Rune399/AEOM/reports and protocols/1. Drukken van knoppen report.pdf

# Drukken van knoppen report

### Sustainability @ Home

Onderzoekers:
Miro Mangelschots - Student Industrieel Ingenieur Industrieel Ontwerpen 2e bachelor Rune Coppieters - Student Industrieel Ingenieur Industrieel Ontwerpen 3e bachelor Kylian Maelstaf - Schakelstudent Industrieel Ingenieur Industrieel Ontwerpen

Zie “1. Drukken van knoppen protocol” voor meer detail over de gebruikte methode en artefacten in dit onderzoek.

# Resultaten

### Eerste eliminatie

Brushless motor: Vraagt veel extra componenten (ESC) en is beter voor toepassingen van hoge snelheid en lage krachtoverbrenging. De brushed DC motor heeft gelijkaardige eigenschappen, maar kan standaard met een tandwielkast geleverd worden, waardoor deze nog niet wordt uitgesloten.

### Testen

Brushed_motor test.mp4 (https://ugentbe-my.sharepoint.com/personal/kylian_maelstaf_ugent_be/Documents/Project%20gebruiksgericht%20ontwerpen/Sustainability%20@%20Home%20-%20Groepswerk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)
Lineair_actuator test.mp4 (https://ugentbe-my.sharepoint.com/personal/kylian_maelstaf_ugent_be/Documents/Project%20gebruiksgericht%20ontwerpen/Sustainability%20@%20Home%20-%20Groepswerk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)
Servo test1.mp4 (https://ugentbe-my.sharepoint.com/personal/kylian_maelstaf_ugent_be/Documents/Project%20gebruiksgericht%20ontwerpen/Sustainability%20@%20Home%20-%20Groepswerk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)
Solenoïde test.mp4 (https://ugentbe-my.sharepoint.com/personal/kylian_maelstaf_ugent_be/Documents/Project%20gebruiksgericht%20ontwerpen/Sustainability%20@%20Home%20-%20Groepswerk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)

# Conclusies

De solenoïde kan makkelijk uitgesloten worden, aangezien dit de enige oplossing was die de knop niet kon indrukken.
De servo heeft maar een matige krachtoverbrenging, voor een matig gewicht en matig gemak van aansturen. De servo is over het algemeen matig, waardoor deze wordt uitgesloten. Het voornaamste voordeel van de servo is echter de aanwezige feedbackloop, die voor hoge precisie en herhaalbaarheid zorgt. Dit weegt echter niet genoeg door, om dit component te kiezen.
De stepper motor wordt uitgesloten, door zijn complexe aansturing en gewicht. De stepper is beter geschikt voor toepassingen waar hoge precisie vereist is (in combinatie met snelheid en >360° draaien).

De lineaire actuator en Brushed DC motor blijven over van oplossingen die zouden volstaan voor de toepassing van knoppen indrukken. Dit is opzig relatief logisch, aangezien de lineaire actuator, in deze proef, een toegepast mechanisme van de brushed DC motor was.
Wat echter wel opvalt bij de specificaties van de beide motoren, is dat de LEGO motor, die gebruikt werd bij de lineaire actuator, veel zwakker is dan de zwakste optie van de DC-motor. Daaruit kan geconcludeerd worden dat de lineaire actuator (= schroefdraad) een grotere krachtomzetting heeft dan het andere mechanisme (glijdend stuk, met off-centre wheel). Om een lager gewicht, voor dezelfde krachtuitvoering te verkrijgen zal de lineaire actuator dus beter zijn… Een bijkomend voordeel is dat lineaire actuator een groet bereik aan posities heeft, terwijl het andere mechanisme eigenlijk maar 2 posities heeft.
Er zal dus verder gewerkt worden met de lineaire actuator.
Kan knop indrukken? | Kracht | Feedbackloop | Gewicht | Gemak aansturen (extra componenten + code)
Servo | Ja | Matig | Ja => hoge precisie + herhaalbaarheid | Matig | Matig
Stepper (niet op knop getest) | ? (Waarschijnlijk) | Matig | Nee (Maar hoge precisie + herhaalbaarheid, bij geen slip) | Zwaar | Moeilijk
Solenoide | Nee | Laag | Nee (niet per se nodig) | Zwaar | Makkelijk
Lineaire actuator | Ja | Zeer Hoog | Nee | Matig | Makkelijk
Brushed + geared | Ja | Zeer Hoog | Nee | Zwaar | Makkelijk
