Rune399/AEOM/reports and protocols/Protocol interview after pivot.pdf

# Protocol user interview (after pivot)

### Sustainability @ Home

Onderzoekers:
Miro Mangelschots - Student Industrieel Ingenieur Industrieel Ontwerpen 2e bachelor Rune Coppieters - Student Industrieel Ingenieur Industrieel Ontwerpen 3

e bachelor
Kylian Maelstaf - Schakelstudent Industrieel Ingenieur Industrieel Ontwerpen

# Kadering en doelstelling

Dit project is begonnen met het thema duurzaam leven thuis, maar is voor ons geëvolueerd tot het automatiseren van “domme apparaten” na een pivot.
Nu hebben we beslist om de focus te verleggen naar de “knoppendrukker”, een toestel die apparaten kan in- / uitschakelen waar een simpele onderbreking van de stroom niet voldoende zou zijn, (zoals bijvoorbeeld bij slimme stekkers) die voordien een deel zou geweest zijn van een groter systeem.
In dit onderzoek willen we onze doelgroep veranderen en ons afvragen waarom deze doelgroep nood zou hebben aan dit apparaat, door middel van interviews waarin we het toestel bespreken en bevragen.
We willen hiermee de volgende onderzoeksvragen beantwoorden:
- Is er interesse in ons product?
- Waar zijn er mogelijkheden tot automatisatie?
- Waar zijn de pains in de automatisatie thuis?
- Is er een meerwaarde tegenover slimme stekkers?

# Verandering doelgroep

We gaan ons verdiepen op de algemene, grote groep mensen in bezit van zonnepanelen die simpelweg willen besparen en geen budget hebben voor batterijen.
Namelijk de mensen die graag hun huis zouden willen “hacken”, mensen die graag met gadgets en technische snufjes bezig zijn en interesse hebben in het automatiseren van hun huis.

# Methode

Gebruikte methodiek: User interview (N=3)
Gebruikte artefacten: Vragenlijst

# Werkwijze

Er zullen een aantal vragen gesteld worden die de volgende onzeker- / onduidelijkheden tracht aan te pakken:
- Zien de gebruikers een meerwaarde in het product, dewelke?
- Is er interesse in het product?
- Meerwaarde tegenover enkel slimme stekkers kopen?
- Wat maakt dit meer dan enkel een coole gadget?
- Hoeveel setuptijd is acceptabel?
- Hoe vaak zouden mensen iets willen automatiseren?
- Wat willen mensen automatiseren?
- Verkopen als bouwpakket?
- Pains identificeren waarop ingespeeld kan worden?
De onderzoeker stelt zicht voor en legt kort de bedoeling van het interview uit.
Bij elke vraag zal er indien mogelijk verdiept worden om de achterliggende intenties / gedachten in kaart te brengen.

## Brede vragen

- Heeft u interesse in het automatiseren van uw huis of bepaalde apparaten? Waarom?
- Bent u bereid hier actief oplossingen voor te zoeken of een artikel voor aan te schaffen?
- Bent u in bezit van voorprogrammeerbare toestellen?
- Indien ja, gebruikt u deze features vaak? Merkt u een aantal mogelijkse tekorten met dat systeem?
- Indien nee, waarom niet?
- Bij welke toestellen / systemen denkt u dat er verdere mogelijkheden zijn voor automatisatie?
- Ochtendroutine?
- Thuiskomen?
- s’ Avonds?
- Is de automatisering van uw wasmachine / droogkast iets die u nuttig zou vinden? Waarom?
- Hoe vaak en wanneer schakelt u deze toestellen in?
- Bent u in bezit van slimme stekkers?
- Waarom wel / niet?
- Merkt u hier beperkingen mee op?
- Zijn er toestellen bij u thuis die niet geautomatiseerd kunnen worden door slimme stekkers?
- (drukknoppen, draaiknoppen, …)
- Zijn er bezorgdheden rondom automatisatie in uw huishouden? Wat moet vermeden worden?
- Hoeveel controle wilt u behouden over automatische acties?
- Bent u actief bezig met het maximaliseren van de opgewekte zonne-energie?
- Schakelt u apparaten in tijdens dat de zon energie oplevert?
- Kunt u een voorbeeld geven van wanneer u uw gedrag aanpast aan zonne-energie?
- Zou u een apparaat die u hierbij helpt effectief gebruiken?

## Gerichte vragen

Hier zullen we een aantal foto’s voorleggen van de knoppendrukker als concept, om een beeld te scheppen over het product.
- Wat zou u ervan vinden moest een toestel fysiek de juiste knoppen drukken om apparaten in/uit te schakelen?
- Zou u zo’n systeem vertrouwen om zelfstandig iets aan / uit te zetten?
- In welke situatie zou dit systeem ongewenst zijn?
- Ziet u een meerwaarde in dit product tegenover slimme stekkers?
- Wat zou dit apparaat moeten doen zodat u het volledig zou vertrouwen?
- Welke zaken zouden het vertrouwen verbreken?
- Wat zou voor u een reden kunnen zijn om dit systeem niet te willen installeren?
- In welke situatie zou een slimme stekker voor u een betere optie zijn?
- Op welk apparaat zou u dit systeem als eerst willen gebruiken?
- Op welk apparaat zou u dit systeem absoluut niet willen toepassen? Waarom?
- Wilt u feedback krijgen over acties die het apparaat uitvoert?
- Indien ja, welke feedback zou relevant zijn? Voor, tijdens of na de actie?
- Indien nee, waarom niet?
- Hoeveel tijd zou u willen spenderen in de setup van dit apparaat?
- Bent u bereid om tools te gebruiken voor een eenmalige setup?
- Geen, meegeleverde of thuis beschikbare tools?
- Zou het interessant zijn om ons product aan te bieden als bouwpakket?
- Componenten apart (ikea)
- Uitbreidingspakket (met extra knoppencontrollers en dergelijke uitbeidingen)

## Concluderend

De onderzoeker rond het gesprek af en bedankt de respondent voor hun medewerking.

# Meting

Dit interview zal via audio opgenomen worden, wat achteraf samen met eventuele notities hernomen kan worden om gemiste items toch nog te vatten.

Zie de report (https://ugentbe-my.sharepoint.com/personal/kylian_maelstaf_ugent_be/Documents/Project%20gebruiksgericht%20ontwerpen/Sustainability%20@%20Home%20-%20Groepswerk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) voor de uitkomst en analyse van dit onderzoek.
