Rune399/AEOM/cad/rotating pivot arm/V2/adjusted.jpg

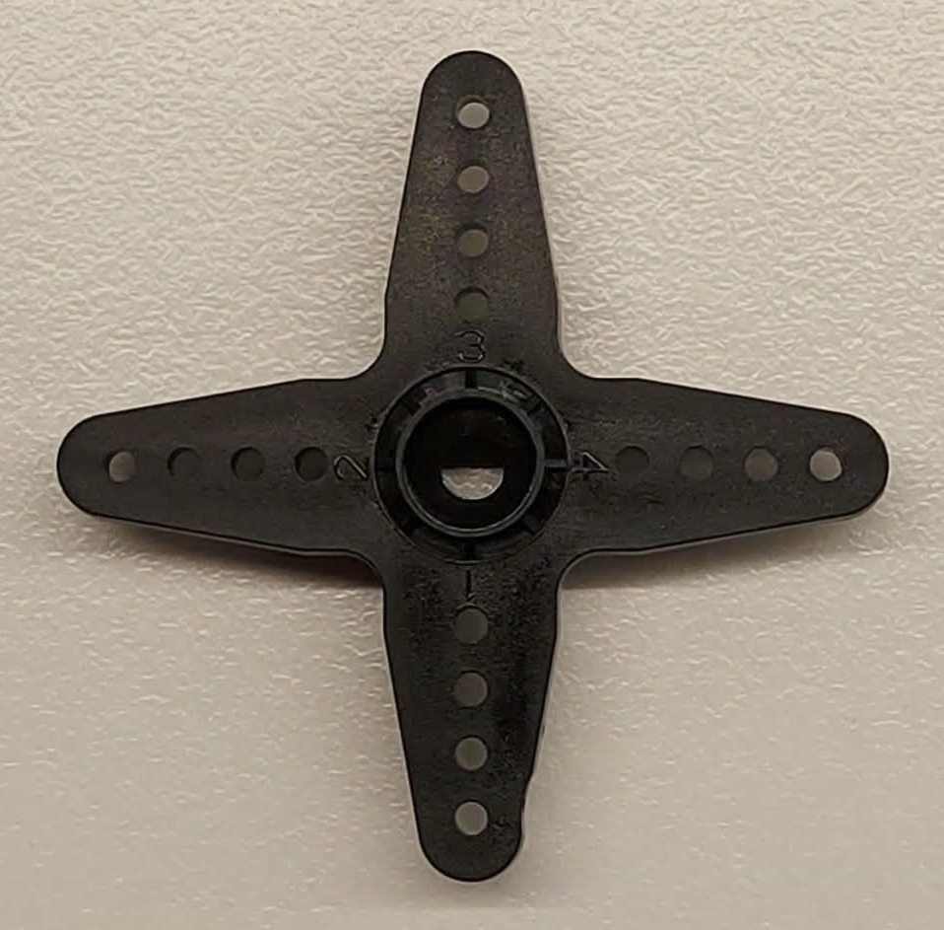
cad/rotating pivot arm/V2/adjusted.jpg
