Rune399/AEOM/img/CMF_Morfologische_kaart.jpg

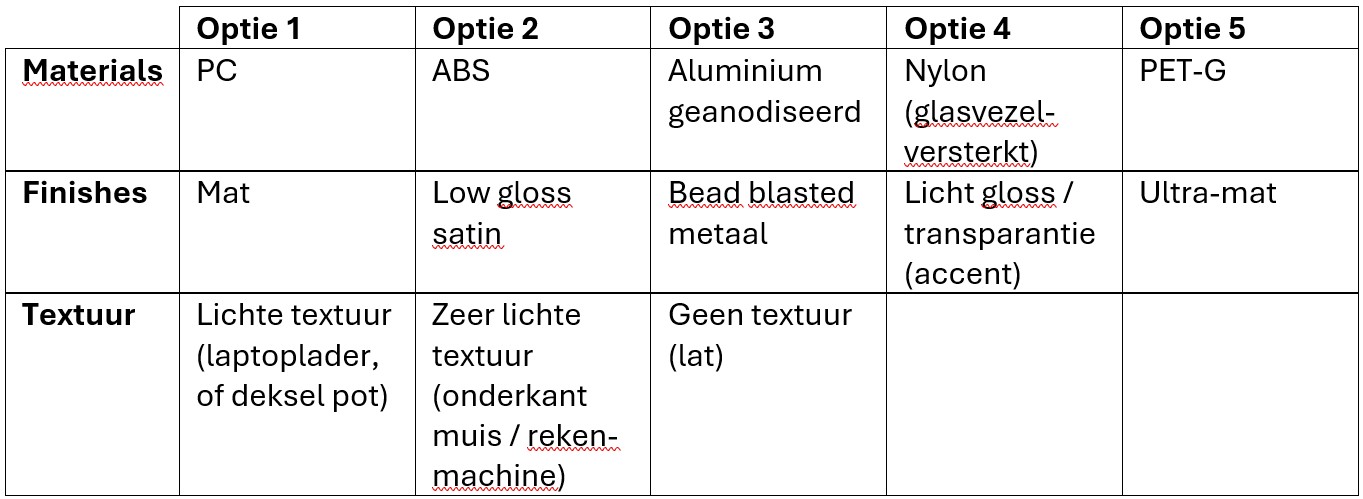
img/CMF_Morfologische_kaart.jpg
