Rune399/AEOM/img/Hero2.png

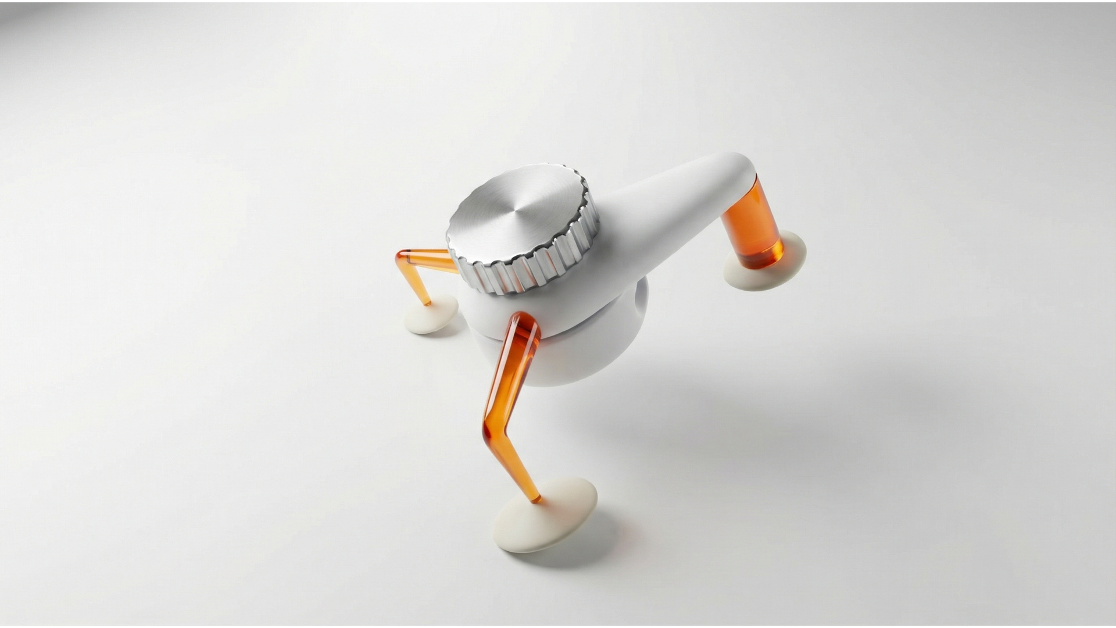
img/Hero2.png
