Rune399/AEOM/img/Interface1 pg3.jpg

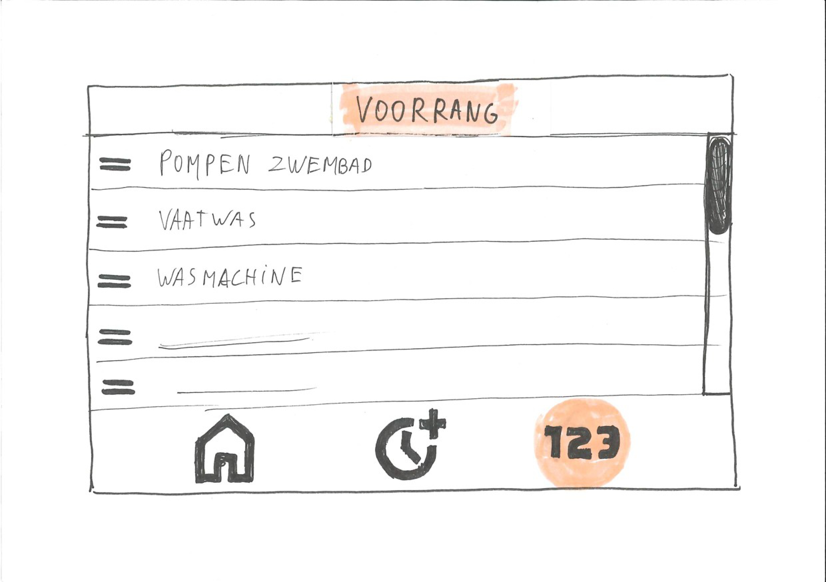
img/Interface1 pg3.jpg
