Rune399/AEOM/img/Interface3 pg1.jpg

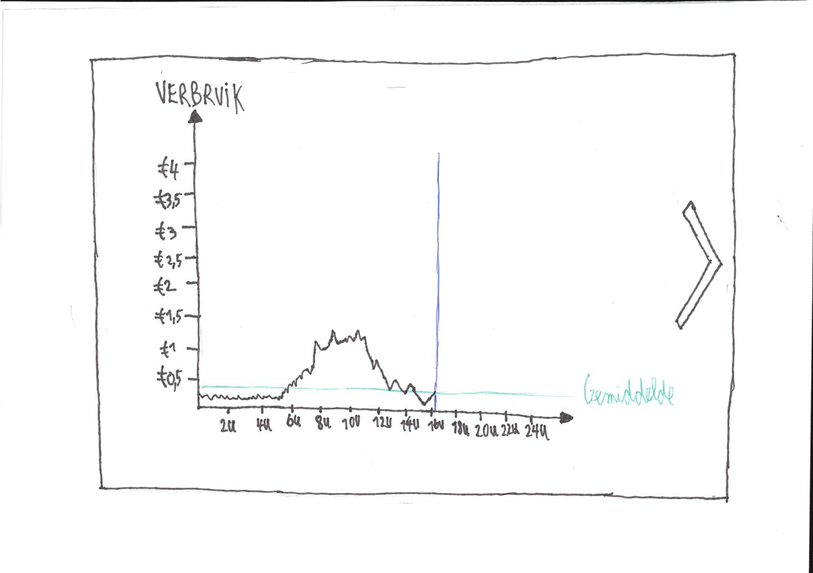
img/Interface3 pg1.jpg
