Rune399/AEOM/img/Interface3 pg3 V2.jpg

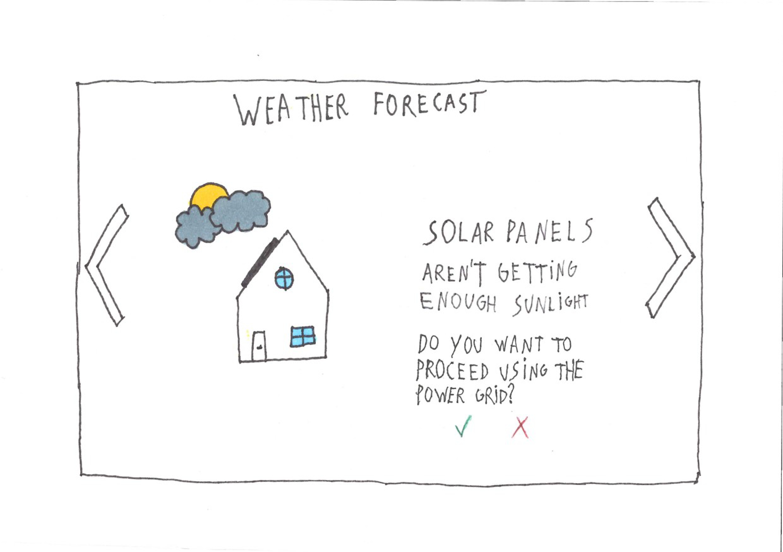
img/Interface3 pg3 V2.jpg
