Rune399/AEOM/img/Interface3 pg4.jpg

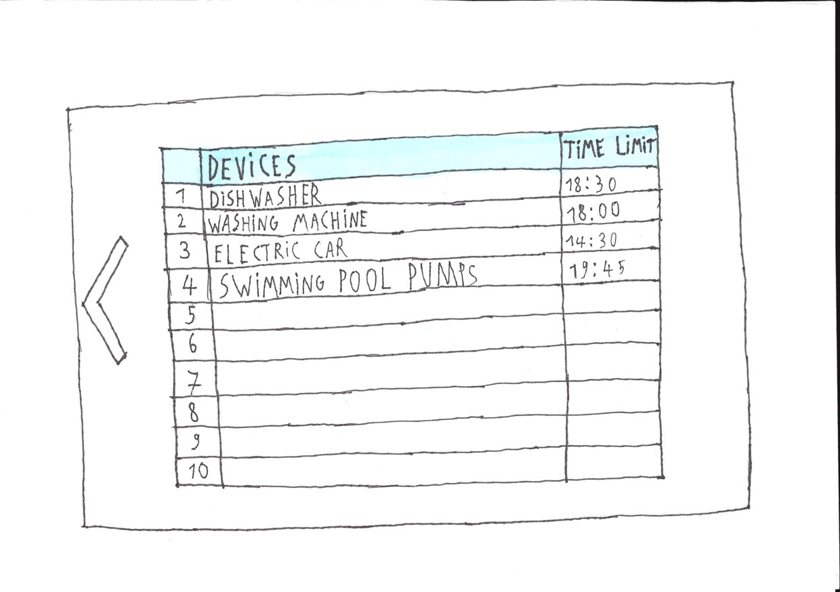
img/Interface3 pg4.jpg
