Rune399/AEOM/img/Interface4 pg2.jpg

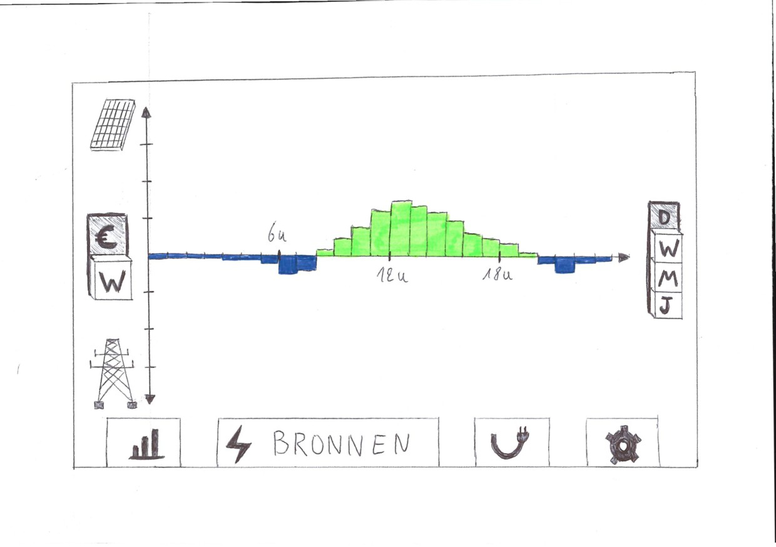
img/Interface4 pg2.jpg
