Rune399/AEOM/img/Interface4 pg3.jpg

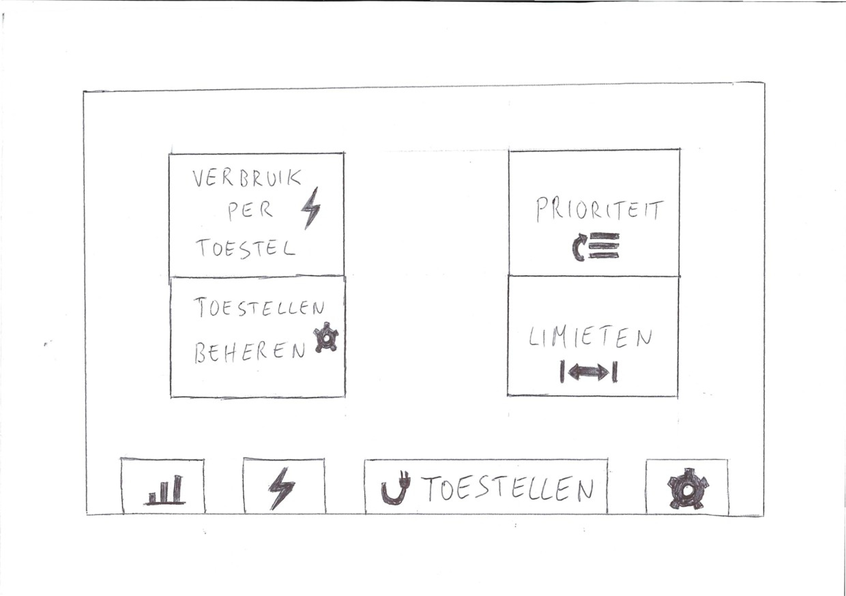
img/Interface4 pg3.jpg
