Rune399/AEOM/img/Interface4 pg4.jpg

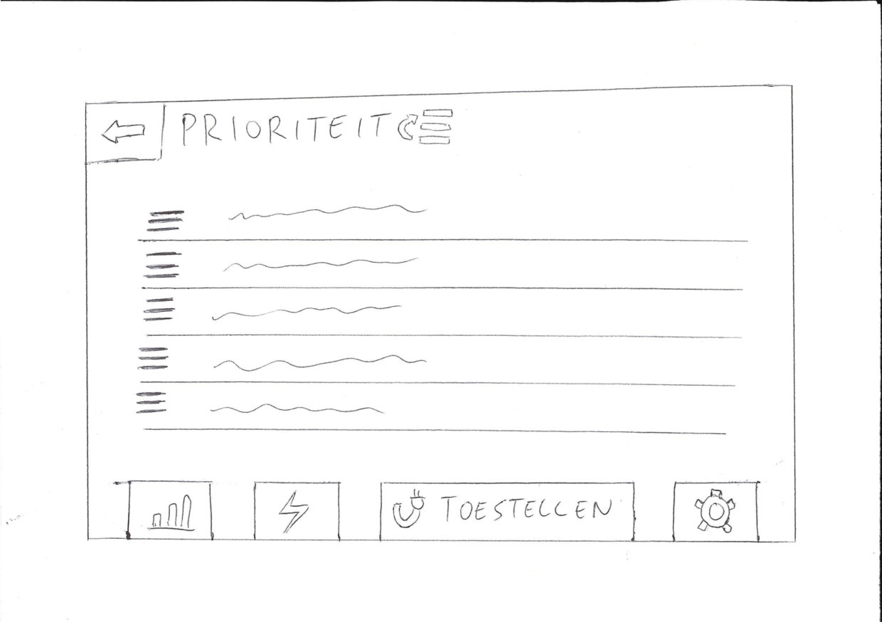
img/Interface4 pg4.jpg
