Rune399/AEOM/img/Interface4 pg5.jpg

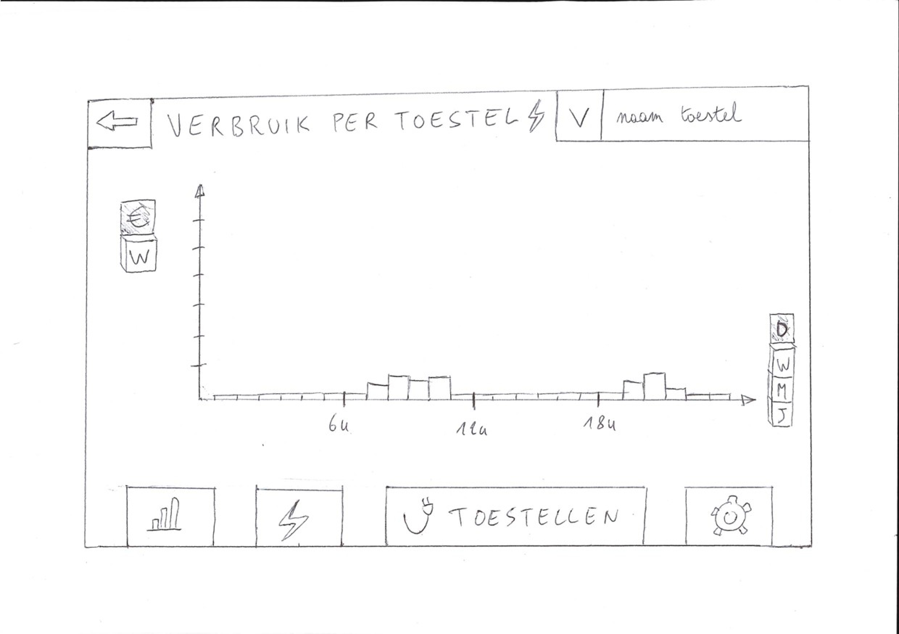
img/Interface4 pg5.jpg
