Rune399/AEOM/cad/rotating slider arm/V1/Robot_Rotating.dxf

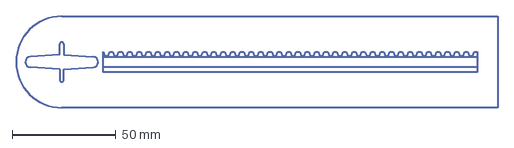
[picture p168: CAD file, 2026-06-12, an earlier design]
cad/rotating slider arm/V1/Robot_Rotating.dxf
232.0 x 44.0 mm
