Rune399/AEOM/cad/rotating pivot arm/V1/DXF lasercut/arm ver - top - 2x.dxf

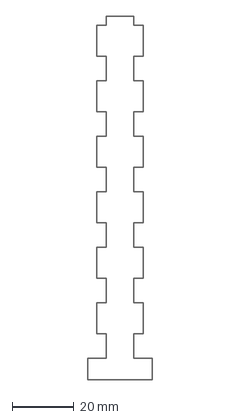
[picture p169: CAD file, 2026-06-12, an earlier design]
cad/rotating pivot arm/V1/DXF lasercut/arm ver - top - 2x.dxf
21.0 x 118.0 mm
