Rune399/AEOM/cad/rotating pivot arm/V1/imported files/SM-S2309S-Arm.SLDPRT

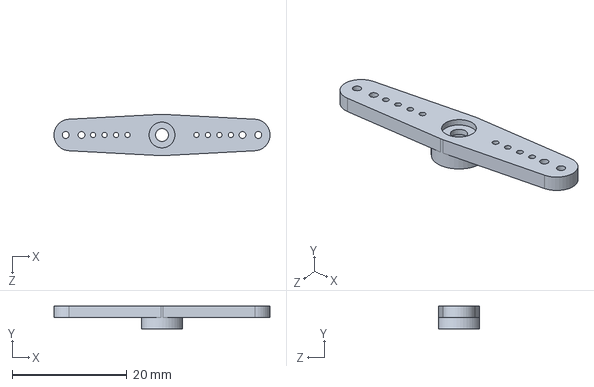
[picture p170: CAD file, 2026-06-12, an earlier design]
cad/rotating pivot arm/V1/imported files/SM-S2309S-Arm.SLDPRT
37.6 x 4.00 x 7.19 mm
